chacharin/robot-arm-design/base.jpg

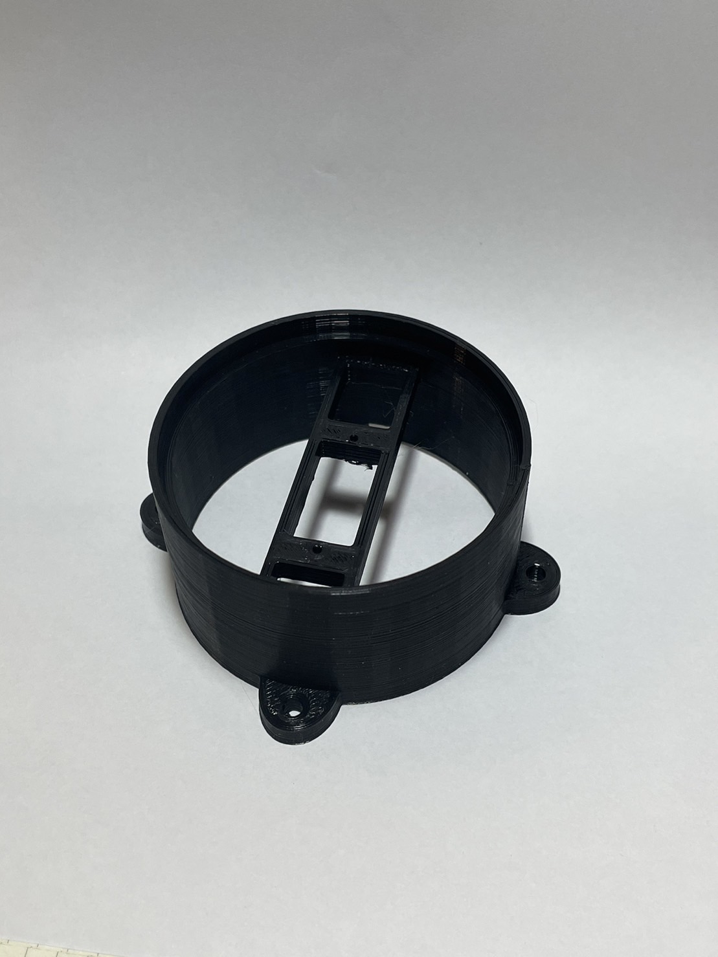
base.jpg
