chacharin/robot-arm-design/body.jpg

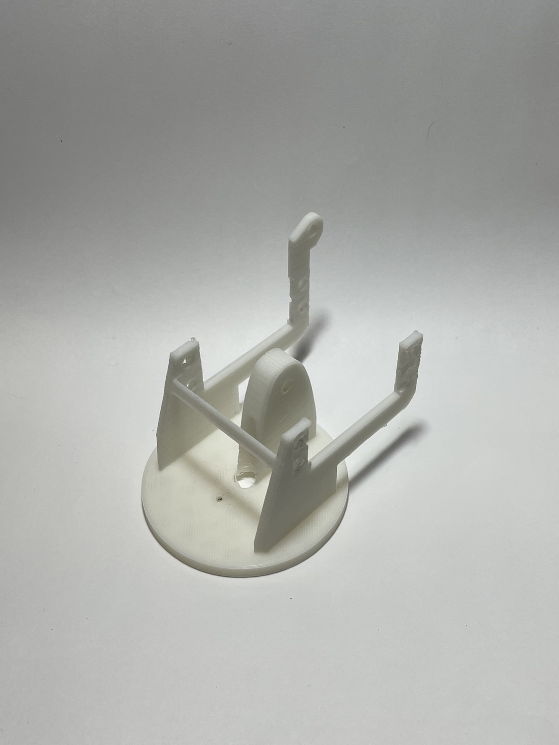
body.jpg
