chacharin/robot-arm-design/full.jpg

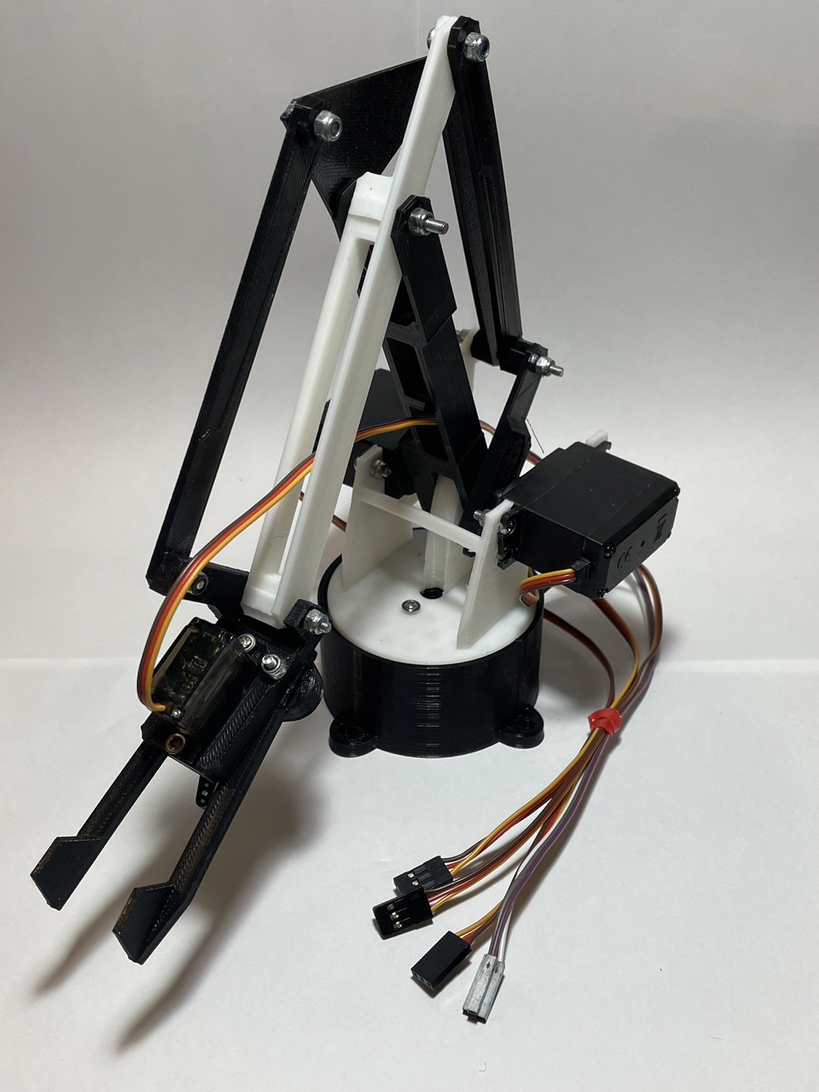
full.jpg
