chacharin/robot-arm-design/gripper-gear.jpg

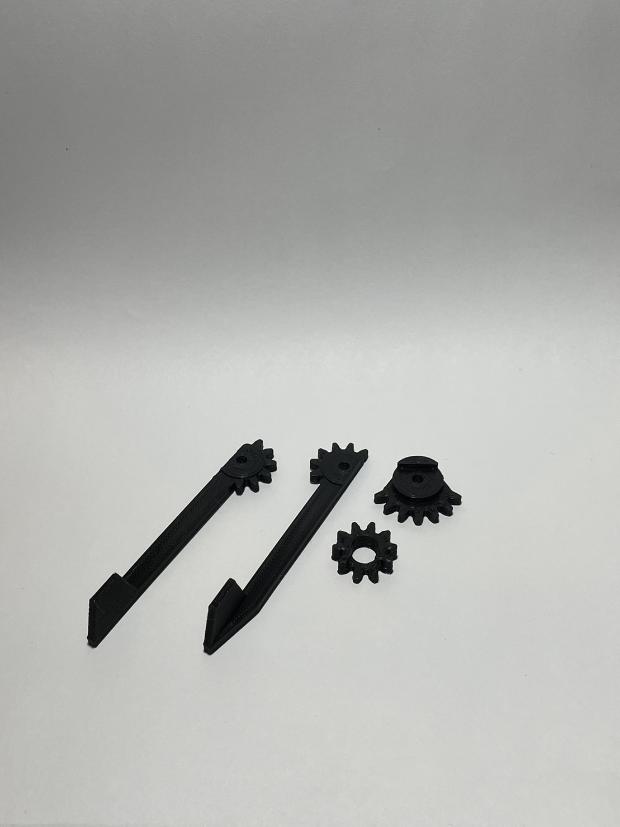
gripper-gear.jpg
