chacharin/robot-arm-design/top-bar.jpg

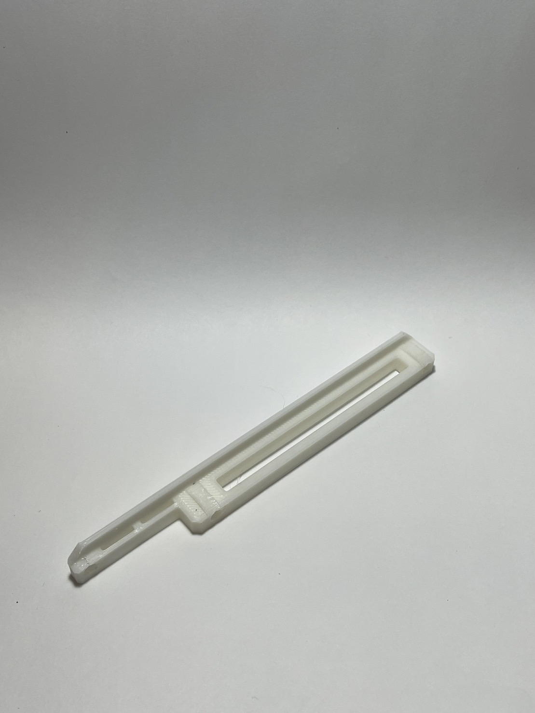
top-bar.jpg
